crmaykish/herring-6502/firmware/src/conway_vga.c

#include <stdlib.h>
#include <stdio.h>
#include <stdint.h>
#include <stdbool.h>
#include <string.h>
#include "herring.h"
#include "serial.h"
#include "vga.h"
#include "delay.h"

#define BOARD_WIDTH (FB_WIDTH / 2)
#define BOARD_HEIGHT (FB_HEIGHT / 2)
#define MAX_GENERATIONS 64
#define RANDOM_SEED_FILL 20

static uint8_t current[BOARD_WIDTH][BOARD_HEIGHT];
static uint8_t previous[BOARD_WIDTH][BOARD_HEIGHT];

static uint8_t cycles;
static uint16_t seed;
static uint8_t i, j;

void init_board();
void draw_board();
void update_state();
uint8_t count_neighbors(uint8_t x, uint8_t y);
void rand_prompt();

void main()
{
    fb_clear();

    printf("Conway's Game of Life\r\n");
    rand_prompt();

    term_clear();

    while (true)
    {
        fb_clear();
        init_board();

        while (cycles <= MAX_GENERATIONS)
        {
            update_state();
            draw_board();
            cycles++;
        }

        delay(200);
    }
}

void init_board()
{
    cycles = 1;

    for (j = 0; j < BOARD_HEIGHT; ++j)
    {
        for (i = 0; i < BOARD_WIDTH; ++i)
        {
            previous[i][j] = ((rand() % 100) < RANDOM_SEED_FILL) ? 1 : 0;
        }
    }
}

void draw_board()
{
    for (j = 0; j < BOARD_HEIGHT; ++j)
    {
        for (i = 0; i < BOARD_WIDTH; ++i)
        {
            FB_SET_PIXEL(i, j, (current[i][j] == 1) ? 2 : 0);
        }
    }

    FB_SWAP_BUFFERS();
}

void update_state()
{
    uint8_t neighbors;

    // Clear current board
    memset(current, 0, BOARD_WIDTH * BOARD_HEIGHT);

    for (j = 0; j < BOARD_HEIGHT; ++j)
    {
        for (i = 0; i < BOARD_WIDTH; ++i)
        {
            neighbors = count_neighbors(i, j);

            if (neighbors == 3 && previous[i][j] == 0)
            {
                // Cell comes alive
                current[i][j] = 1;
            }
            else if ((neighbors == 2 || neighbors == 3) && previous[i][j] == 1)
            {
                // Cell stays alive
                current[i][j] = 1;
            }
            else
            {
                // Cell dies
                current[i][j] = 0;
            }
        }
    }

    // Copy current board to previous
    memcpy(previous, current, BOARD_WIDTH * BOARD_HEIGHT);
}

uint8_t count_neighbors(uint8_t x, uint8_t y)
{
    // Living neighbors
    uint8_t living = 0;

    if (x > 0 && y > 0)
        living += previous[x - 1][y - 1];

    if (x > 0)
        living += previous[x - 1][y];

    if (x > 0 && y < BOARD_HEIGHT - 1)
        living += previous[x - 1][y + 1];

    if (y > 0)
        living += previous[x][y - 1];

    if (y < BOARD_HEIGHT - 1)
        living += previous[x][y + 1];

    if (x < BOARD_WIDTH - 1 && y > 0)
        living += previous[x + 1][y - 1];

    if (x < BOARD_WIDTH - 1)
        living += previous[x + 1][y];

    if (x < BOARD_WIDTH - 1 && y < BOARD_HEIGHT - 1)
        living += previous[x + 1][y + 1];

    return living;
}

void rand_prompt()
{
    uint8_t seed_count = 0;

    printf("Enter some random characters:\r\n");

    while (seed_count < 10)
    {
        seed += serial_getc();
        seed <<= 1;
        printf(".");
        seed_count++;
    }

    srand(seed);
}
