crmaykish/herring-6502/pld/gpu_framebuffer/vga_timing.v

module vga_timing(CLK_PIXEL, Hs, Vs, SCREEN_X, SCREEN_Y, ON_SCREEN);
    input CLK_PIXEL;
    output reg Hs, Vs;

    output reg [10:0] SCREEN_X;
    output reg [10:0] SCREEN_Y;

    output reg ON_SCREEN;

    parameter HA_END = 1023;
    parameter HS_STA = HA_END + 24;
    parameter HS_END = HS_STA + 136;
    parameter LINE = 1343;

    parameter VA_END = 767;
    parameter VS_STA = VA_END + 3;
    parameter VS_END = VS_STA + 6;
    parameter SCREEN = 805;

    always @(posedge CLK_PIXEL) begin
        if (SCREEN_X == LINE)
            begin
                SCREEN_X <= 0;
                SCREEN_Y <= (SCREEN_Y == SCREEN) ? 0 : SCREEN_Y + 1;
            end
        else
            begin
                SCREEN_X <= SCREEN_X + 1;
            end
    end

    always @(posedge CLK_PIXEL) begin
        Hs <= ~(SCREEN_X >= HS_STA && SCREEN_X < HS_END);
        Vs <= ~(SCREEN_Y >= VS_STA && SCREEN_Y < VS_END);
        ON_SCREEN <= (SCREEN_X <= HA_END) && (SCREEN_Y <= VA_END);
    end

endmodule
