crmaykish/herring-6502/firmware/crt0.asm

.export   _init, _exit
.import   _main

.export   __STARTUP__ : absolute = 1        ; Mark as startup
.import   __RAM_START__, __RAM_SIZE__       ; Linker generated

.import    copydata, zerobss, initlib, donelib

.include  "zeropage.inc"

.segment "VECTORS"

    .addr $DEAD
    .addr _init
    .addr $BEEF

.segment  "STARTUP"

_init:   
          SEI
          LDX     #$FF                 ; Initialize stack pointer to $01FF
          TXS
          CLD                          ; Clear decimal mode

          LDA     #<(__RAM_START__ + __RAM_SIZE__)
          STA     sp
          LDA     #>(__RAM_START__ + __RAM_SIZE__)
          STA     sp+1

          JSR     zerobss              ; Clear BSS segment
          JSR     copydata             ; Initialize DATA segment
          JSR     initlib              ; Run constructors

          JSR     _main

_exit:    JSR     donelib              ; Run destructors
          BRK
